fbradasc/GRUB/GRUB.kicad_sch

## KiCad design GRUB.kicad_sch (2025-01-13, an earlier design)

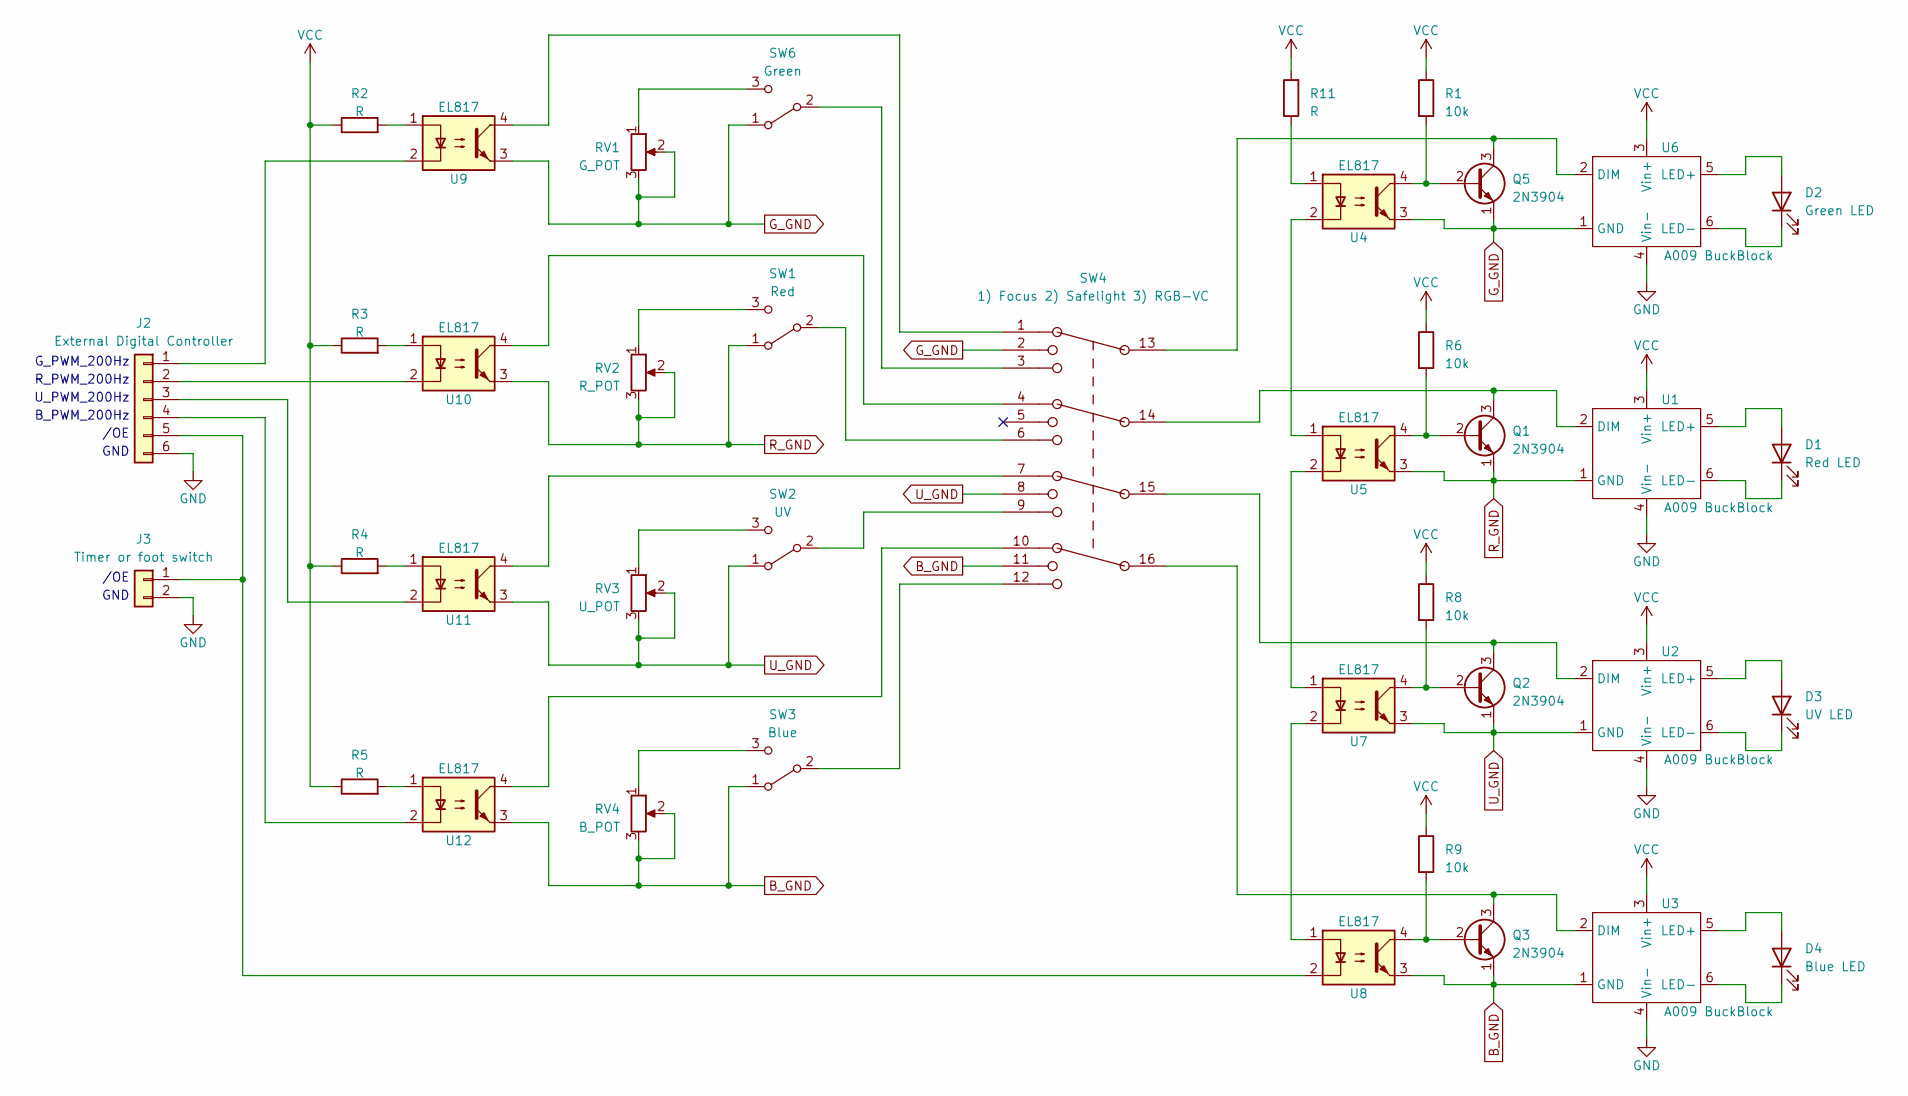
[picture p6: schematic GRUB.kicad_sch]

Parts:
D1: Red LED
D2: Green LED
D3: UV LED
D4: Blue LED
J2: External Digital Controller
J3: Timer or foot switch
Q1, Q2, Q3, Q5: 2N3904; TO-92_Molded_Narrow
R1, R6, R8, R9: 10k
R2, R3, R4, R5, R11: R
RV1: G_POT
RV2: R_POT
RV3: U_POT
RV4: B_POT
SW1: Red
SW2: UV
SW3: Blue
SW4: 1) Focus 2) Safelight 3) RGB-VC
SW6: Green
U1, U2, U3, U6: A009 BuckBlock
U4, U5, U7, U8, U9, U10, U11, U12: EL817; DIP-4_W7.62mm

Connections:
B_GND: Q3.1 (E), RV4.2, RV4.3, SW3.1 (A), SW4.11, U3.1 (GND), U8.3, U12.3
GND: J2.6, J3.2, U1.4 (Vin-), U2.4 (Vin-), U3.4 (Vin-), U6.4 (Vin-)
G_GND: Q5.1 (E), RV1.2, RV1.3, SW4.2, SW6.1 (A), U4.3, U6.1 (GND), U9.3
unnamed: D1.1 (K), U1.6 (LED-)
unnamed: D1.2 (A), U1.5 (LED+)
unnamed: D2.1 (K), U6.6 (LED-)
unnamed: D2.2 (A), U6.5 (LED+)
unnamed: D3.1 (K), U2.6 (LED-)
unnamed: D3.2 (A), U2.5 (LED+)
unnamed: D4.1 (K), U3.6 (LED-)
unnamed: D4.2 (A), U3.5 (LED+)
unnamed: J2.1, U9.2
unnamed: J2.2, U10.2
unnamed: J2.3, U11.2
unnamed: J2.4, U12.2
unnamed: J2.5, J3.1, U8.2
unnamed: Q1.2 (B), R6.2, U5.4
unnamed: Q1.3 (C), SW4.14, U1.2 (DIM)
unnamed: Q2.2 (B), R8.2, U7.4
unnamed: Q2.3 (C), SW4.15, U2.2 (DIM)
unnamed: Q3.2 (B), R9.2, U8.4
unnamed: Q3.3 (C), SW4.16, U3.2 (DIM)
unnamed: Q5.2 (B), R1.2, U4.4
unnamed: Q5.3 (C), SW4.13, U6.2 (DIM)
unnamed: R2.2, U9.1
unnamed: R3.2, U10.1
unnamed: R4.2, U11.1
unnamed: R5.2, U12.1
unnamed: R11.1, U4.1
unnamed: RV1.1, SW6.3 (C)
unnamed: RV2.1, SW1.3 (C)
unnamed: RV3.1, SW2.3 (C)
unnamed: RV4.1, SW3.3 (C)
unnamed: SW1.2 (B), SW4.6
unnamed: SW2.2 (B), SW4.9
unnamed: SW3.2 (B), SW4.12
unnamed: SW4.1, U9.4
unnamed: SW4.3, SW6.2 (B)
unnamed: SW4.4, U10.4
unnamed: SW4.7, U11.4
unnamed: SW4.10, U12.4
unnamed: U4.2, U5.1
unnamed: U5.2, U7.1
unnamed: U7.2, U8.1
R_GND: Q1.1 (E), RV2.2, RV2.3, SW1.1 (A), U1.1 (GND), U5.3, U10.3
U_GND: Q2.1 (E), RV3.2, RV3.3, SW2.1 (A), SW4.8, U2.1 (GND), U7.3, U11.3
VCC: R1.1, R2.1, R3.1, R4.1, R5.1, R6.1, R8.1, R9.1, R11.2, U1.3 (Vin+), U2.3 (Vin+), U3.3 (Vin+), U6.3 (Vin+)

Notes on the sheet:
GND
B_PWM_200Hz
/OE
R_PWM_200Hz
U_PWM_200Hz
G_PWM_200Hz
